kyuditsky/AFE/images/afe_diff_r20_a.png

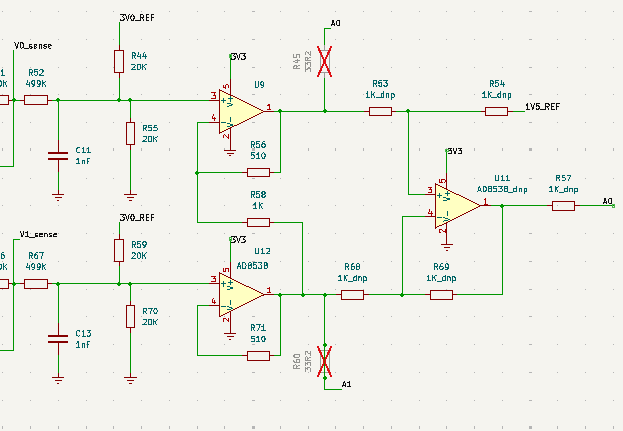
images/afe_diff_r20_a.png
