kyuditsky/AFE/images/afe_diff_r20_b.png

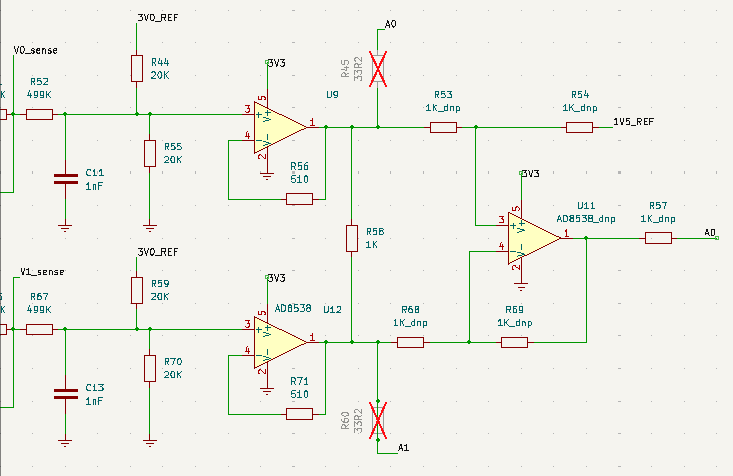
images/afe_diff_r20_b.png
