kyuditsky/AFE/images/alt_layout_BP 2025-01-16 at 12.59.53 PM.png

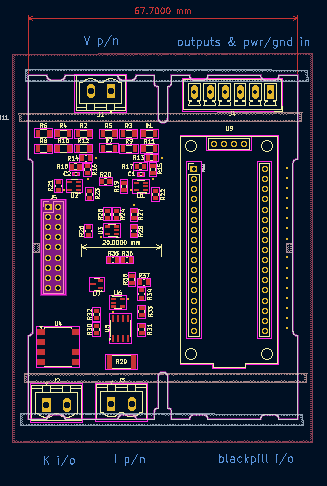
images/alt_layout_BP 2025-01-16 at 12.59.53 PM.png
