kyuditsky/AFE/images/Better_alt_layout 2025-01-16 at 1.14.08 PM.png

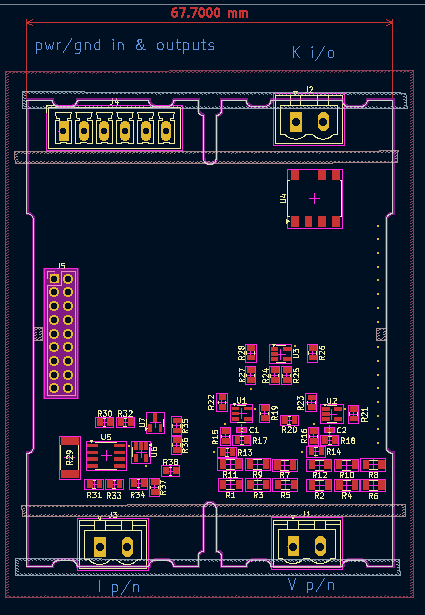
images/Better_alt_layout 2025-01-16 at 1.14.08 PM.png
