kyuditsky/AFE/images/Fusion/connector 2025-01-24 at 3.17.53 PM.png

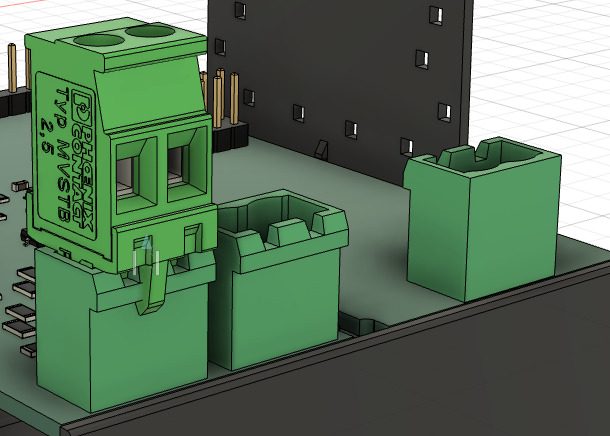
images/Fusion/connector 2025-01-24 at 3.17.53 PM.png
