kyuditsky/AFE/images/Fusion/wide 2025-01-24 at 4.24.46 PM.png

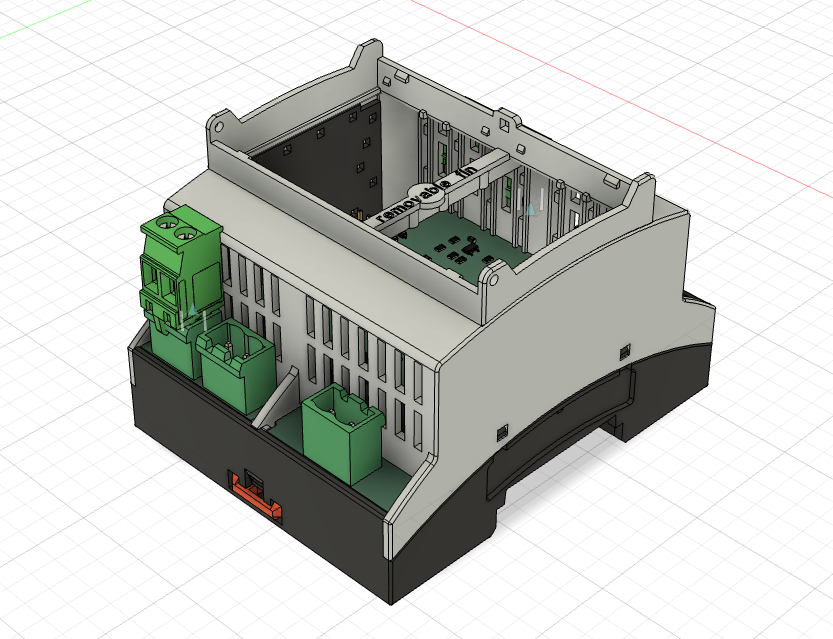
images/Fusion/wide 2025-01-24 at 4.24.46 PM.png
