kyuditsky/AFE/images/HBUS_/Screenshot 2025-01-16 at 11.58.58 AM.png

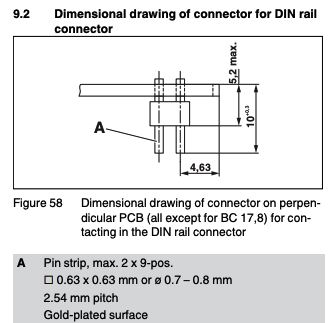
images/HBUS_/Screenshot 2025-01-16 at 11.58.58 AM.png
