kyuditsky/AFE/images/HBUS_/Screenshot 2025-01-16 at 12.01.28 PM.png

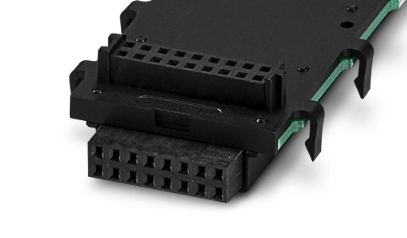
images/HBUS_/Screenshot 2025-01-16 at 12.01.28 PM.png
