kyuditsky/AFE/images/HBUS_/updated_HBUSheader.png

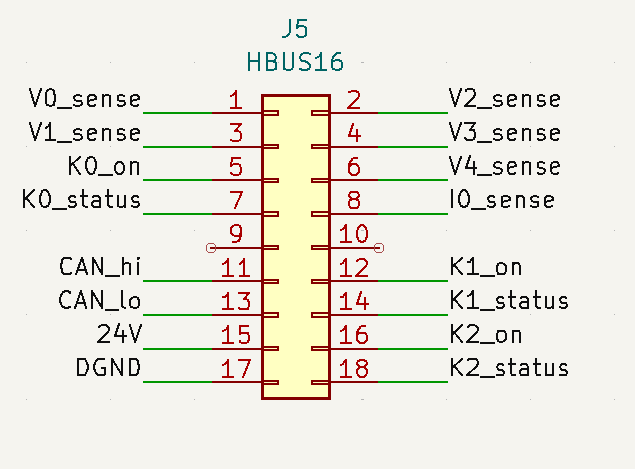
images/HBUS_/updated_HBUSheader.png
