kyuditsky/AFE/images/layout_2025-01-15 at 5.03.08 PM.png

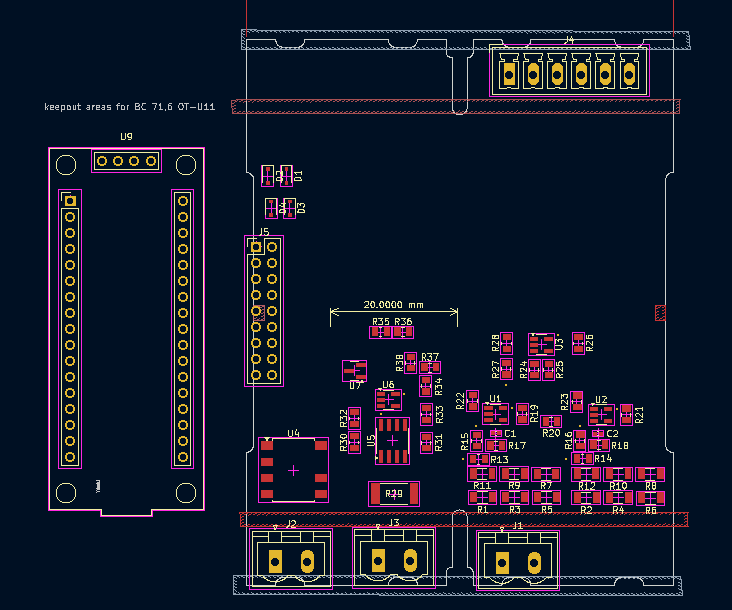
images/layout_2025-01-15 at 5.03.08 PM.png
