kyuditsky/AFE/images/ratsnest_2025-01-15 at 2.41.12 PM.png

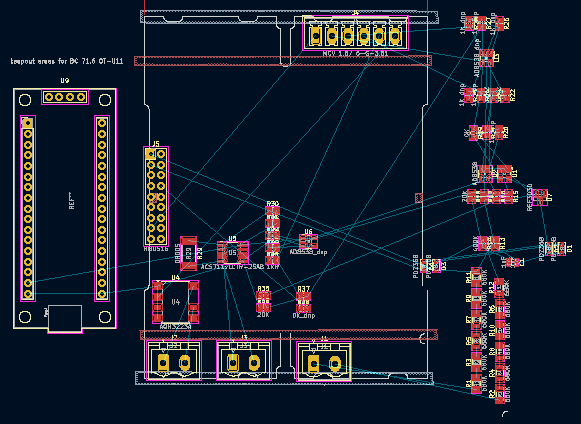
images/ratsnest_2025-01-15 at 2.41.12 PM.png
