kyuditsky/AFE/images/screenshots/Screenshot 2025-01-21 at 9.37.03 PM.png

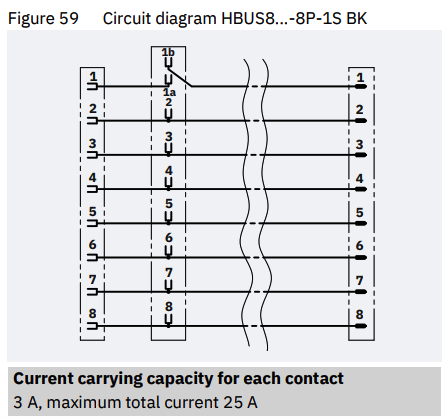
images/screenshots/Screenshot 2025-01-21 at 9.37.03 PM.png
