kyuditsky/AFE/images/screenshots/Screenshot 2025-01-22 at 2.51.09 PM.png

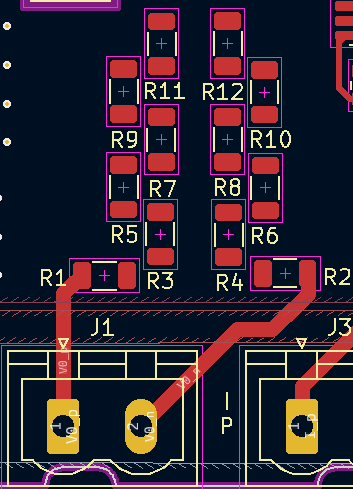
images/screenshots/Screenshot 2025-01-22 at 2.51.09 PM.png
