kyuditsky/AFE/images/screenshots/Screenshot 2025-01-24 at 3.53.09 PM.png

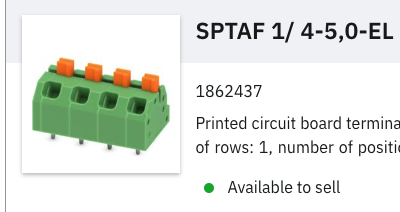
images/screenshots/Screenshot 2025-01-24 at 3.53.09 PM.png
