kyuditsky/AFE/images/screenshots/Screenshot 2025-01-24 at 9.54.24 AM.png

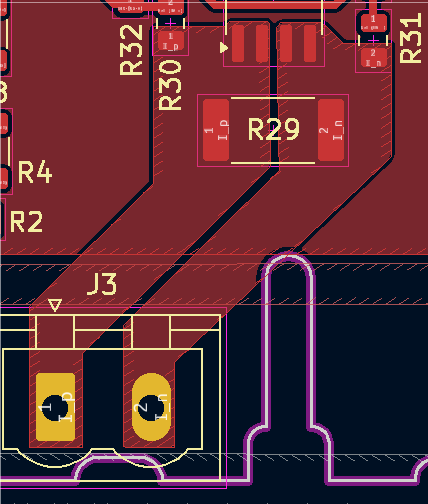
images/screenshots/Screenshot 2025-01-24 at 9.54.24 AM.png
