kyuditsky/AFE/afe_230v_16a_main/testingrev2/single_A0A1_5v10khz.png

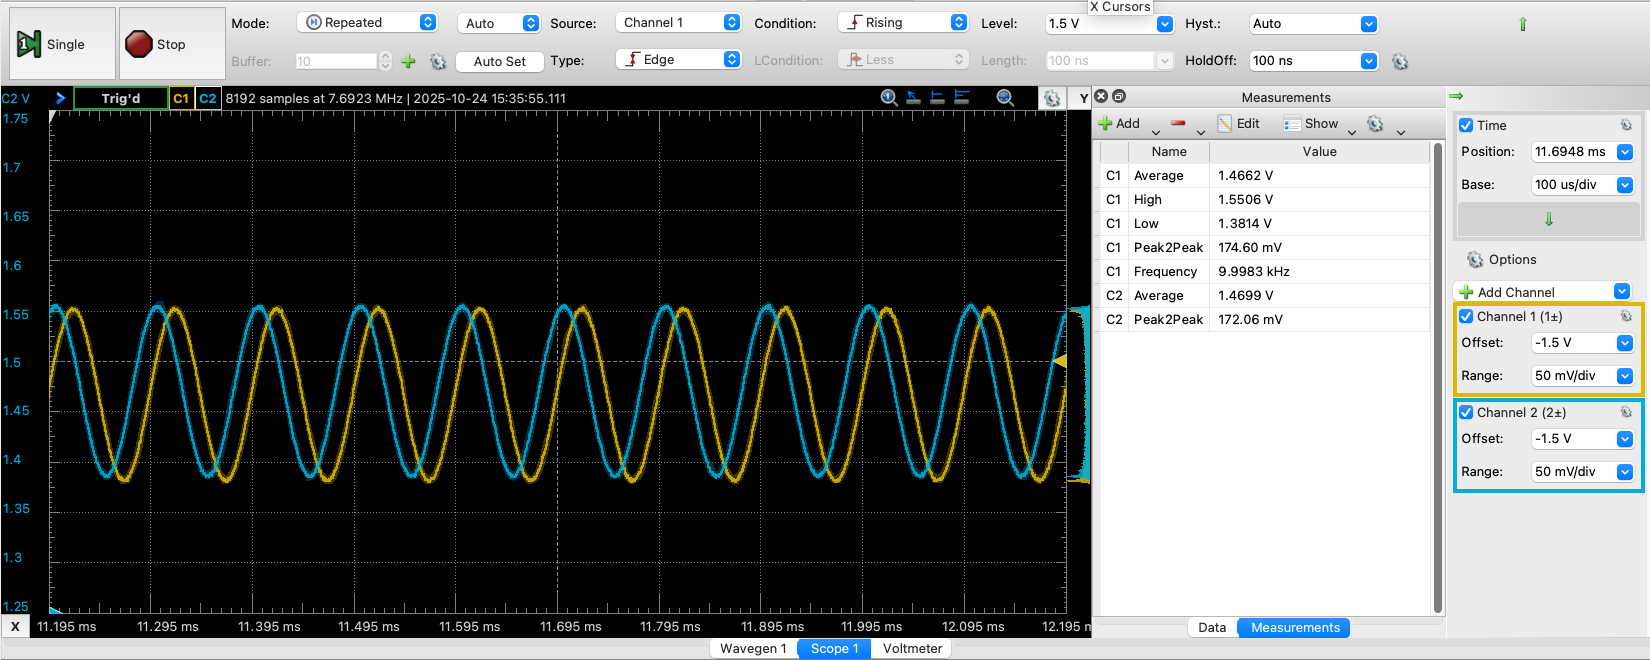
afe_230v_16a_main/testingrev2/single_A0A1_5v10khz.png
